mistic100/Nixie-Clock/Model 2025/indic+support.SLDASM

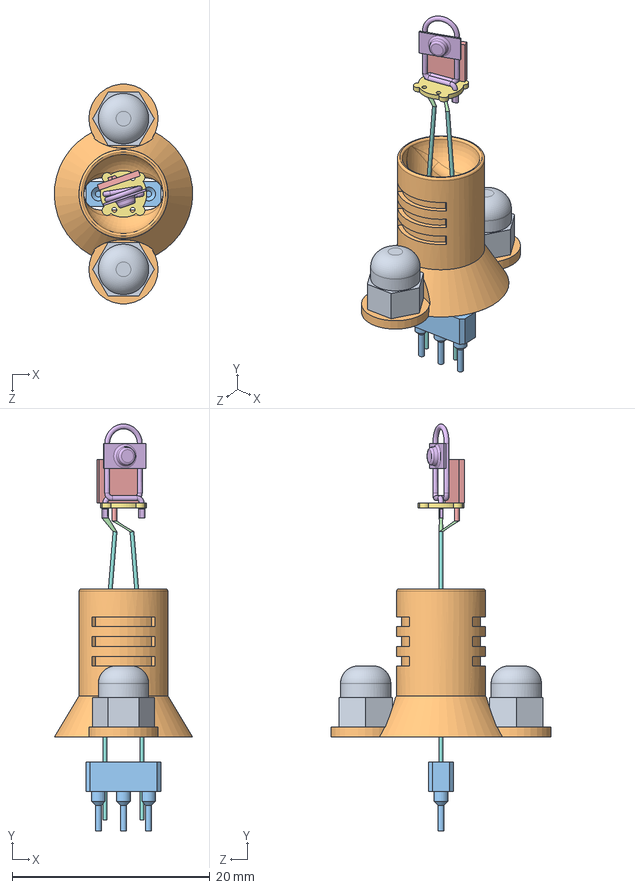
[picture p71: CAD file, 2025-04-05]
Model 2025/indic+support.SLDASM
14.0 x 41.2 x 22.2 mm
NX-SZP-IN3-02-v01 x 2
NX-SZP-IN3-03-v01
NX-SZP-IN3-04-v01
NX-SZP-IN3-05-v01
NX-SZP-IN3-06-v01
tulipex2
cache-indic
ecrou borgne x 2
