mistic100/Nixie-Clock/Model 2025/NX-SZP-IN3/NX-SZP-IN3-03-v01.SLDPRT

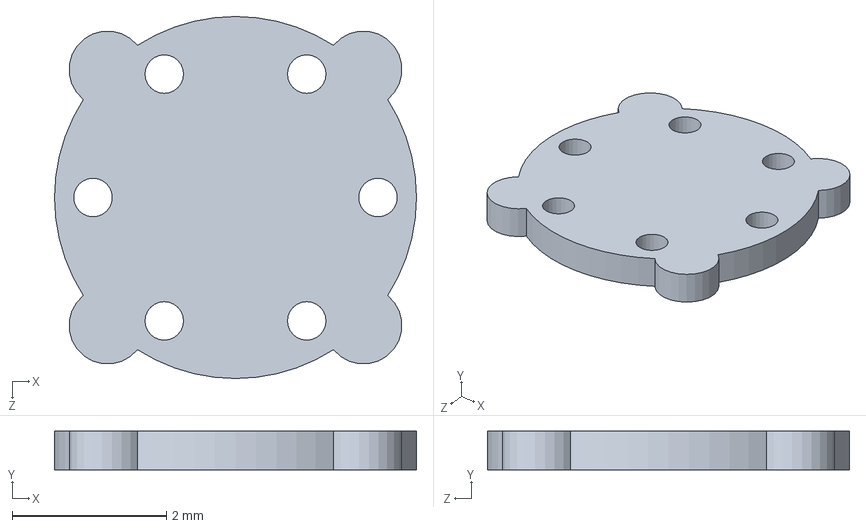
[picture p81: CAD file, 2025-04-05]
Model 2025/NX-SZP-IN3/NX-SZP-IN3-03-v01.SLDPRT
4.70 x 0.5 x 4.70 mm
