mistic100/Nixie-Clock/Model 2025/tulipex2.SLDPRT

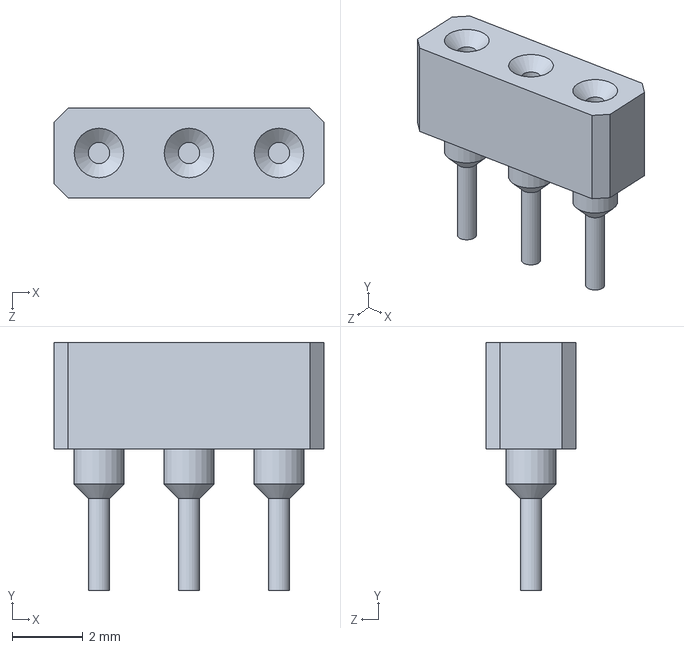
[picture p82: CAD file, 2025-04-05]
Model 2025/tulipex2.SLDPRT
7.62 x 7.00 x 2.54 mm
