mistic100/Nixie-Clock/Model 2025/calle-tube.SLDPRT

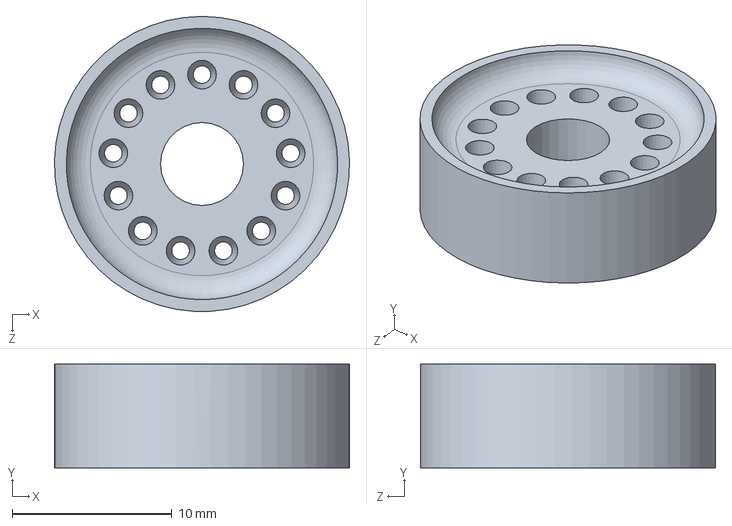
[picture p83: CAD file, 2025-04-05]
Model 2025/calle-tube.SLDPRT
18.5 x 6.50 x 18.5 mm
