mistic100/Nixie-Clock/Model 2025/NX-SZP-IN14/NX-SZP-IN14-15-v01.SLDPRT

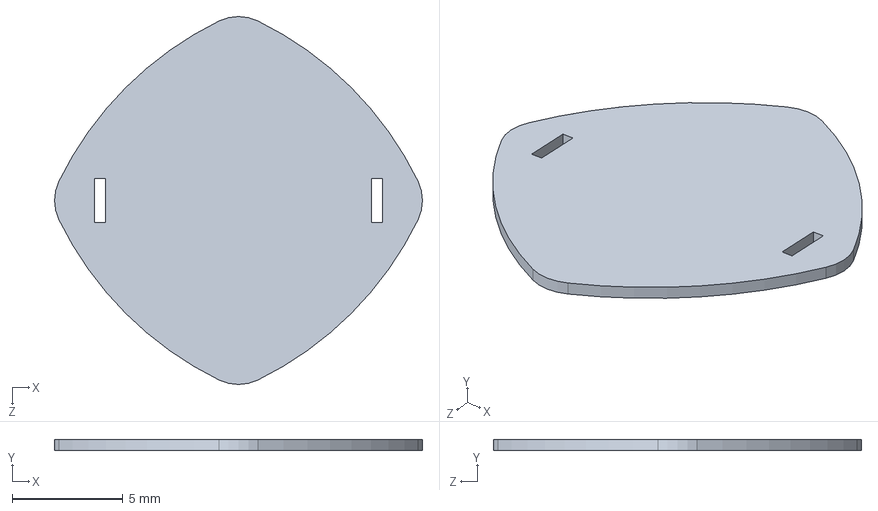
[picture p84: CAD file, 2025-04-05]
Model 2025/NX-SZP-IN14/NX-SZP-IN14-15-v01.SLDPRT
16.6 x 0.5 x 16.6 mm
