mistic100/Nixie-Clock/Model 2025/NX-SZP-IN3/NX-SZP-IN3-06-v01.SLDPRT

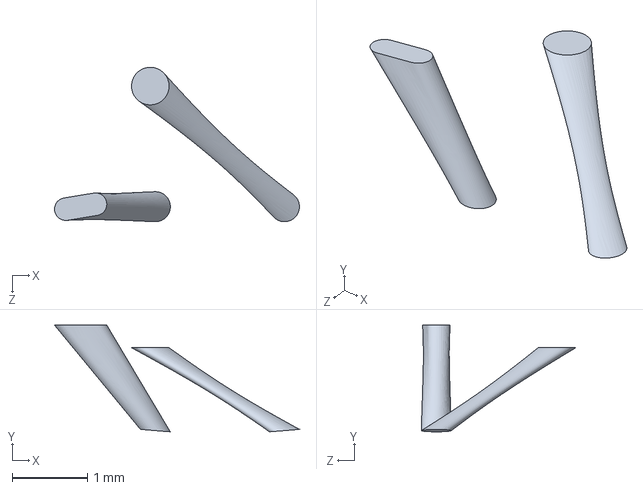
[picture p85: CAD file, 2025-04-05]
Model 2025/NX-SZP-IN3/NX-SZP-IN3-06-v01.SLDPRT
3.25 x 1.42 x 2.05 mm
