mistic100/Nixie-Clock/Model/cover.SLDPRT

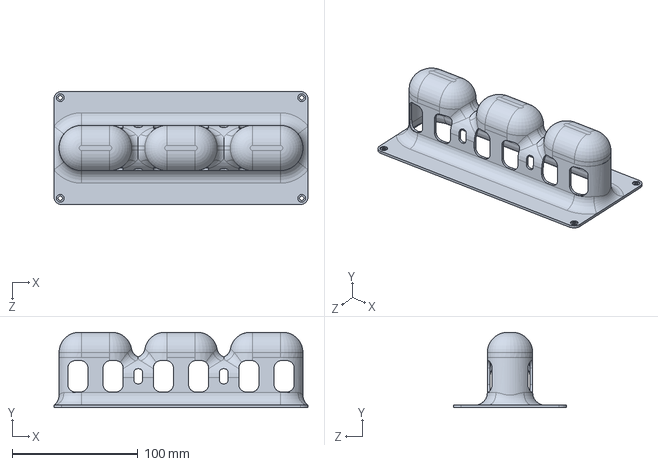
[picture p86: CAD file, 2020-09-19]
Model/cover.SLDPRT
202.0 x 60.0 x 90.0 mm
