mistic100/Nixie-Clock/Model 2025/foot.SLDPRT

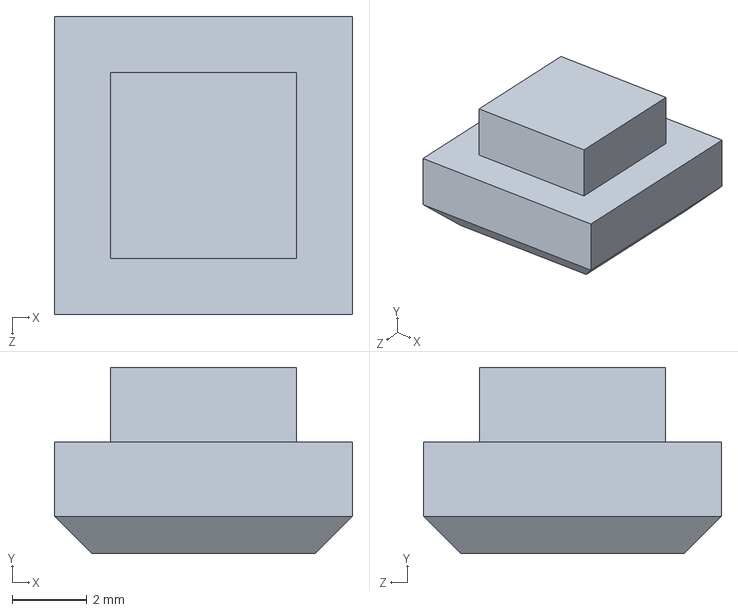
[picture p87: CAD file, 2025-04-05]
Model 2025/foot.SLDPRT
8.00 x 5.00 x 8.00 mm
