mistic100/Nixie-Clock/Model 2025/NX-SZP-IN3/NX-SZP-IN3-04-v01.SLDPRT

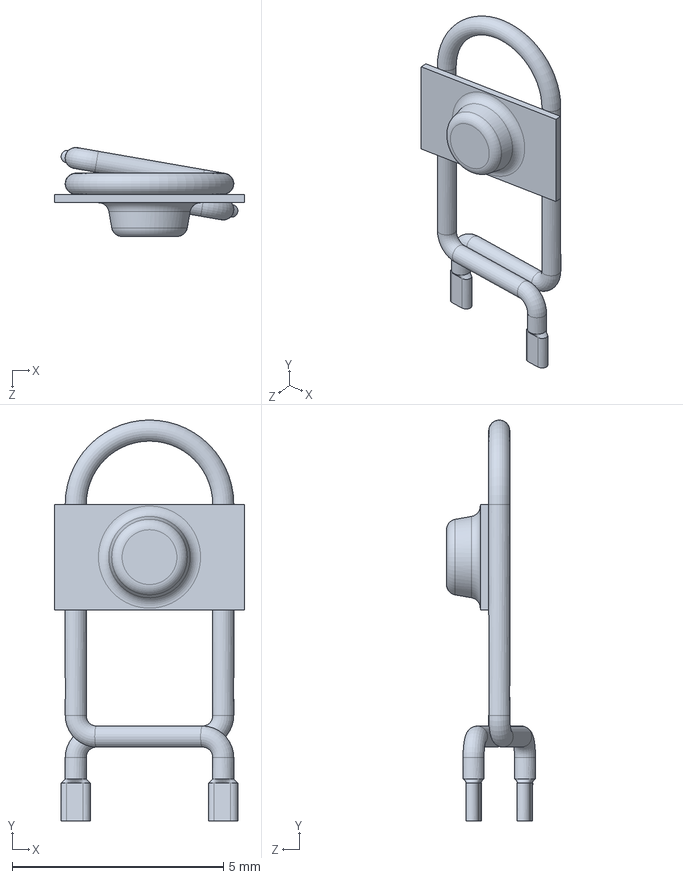
[picture p88: CAD file, 2025-04-05]
Model 2025/NX-SZP-IN3/NX-SZP-IN3-04-v01.SLDPRT
4.50 x 9.50 x 2.11 mm
