mistic100/Nixie-Clock/Model/pied.SLDPRT

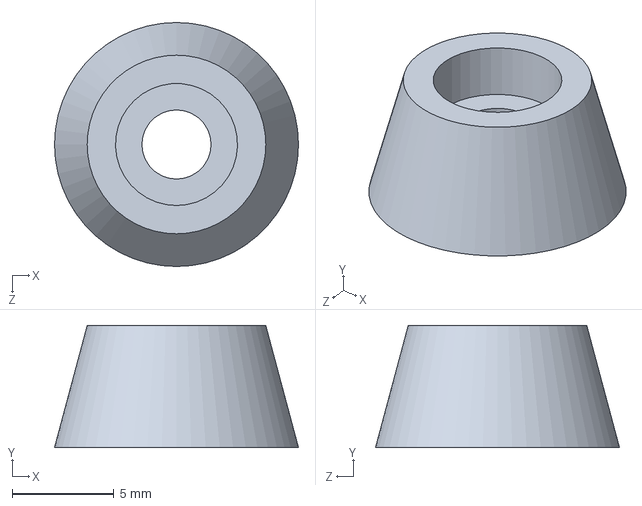
[picture p89: CAD file, 2020-06-08]
Model/pied.SLDPRT
12.0 x 6.00 x 12.0 mm
