mistic100/Nixie-Clock/Model/buttons-plate.SLDPRT

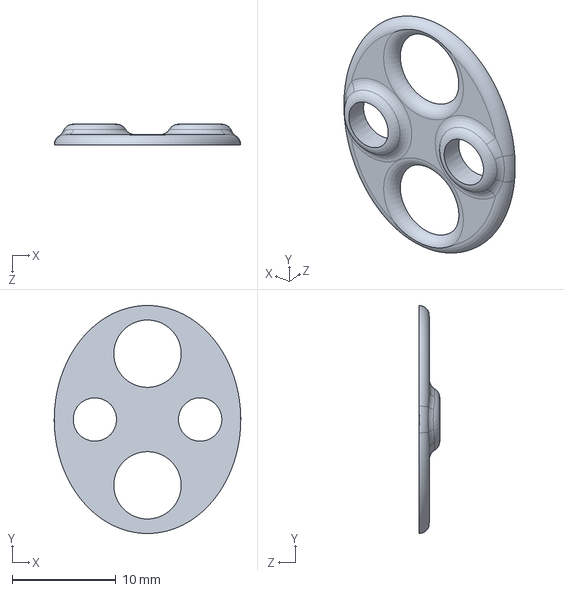
[picture p91: CAD file, 2020-06-06]
Model/buttons-plate.SLDPRT
18.0 x 22.0 x 2.00 mm
