mistic100/Nixie-Clock/Model 2025/NX-SZP-IN14/NX-SZP-IN14-20-v01.SLDPRT

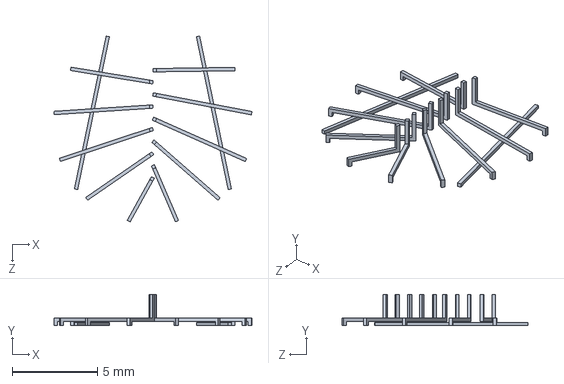
[picture p92: CAD file, 2025-04-05]
Model 2025/NX-SZP-IN14/NX-SZP-IN14-20-v01.SLDPRT
11.6 x 1.85 x 10.9 mm
