mistic100/Nixie-Clock/Model 2025/pcb.SLDPRT

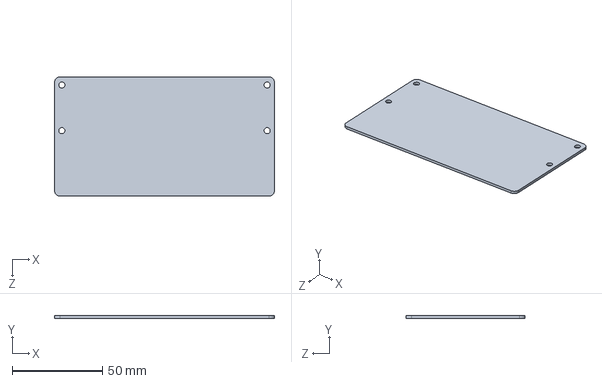
[picture p93: CAD file, 2025-04-05]
Model 2025/pcb.SLDPRT
121.6 x 1.50 x 65.9 mm
