mistic100/Nixie-Clock/Model 2025/plaque.SLDPRT

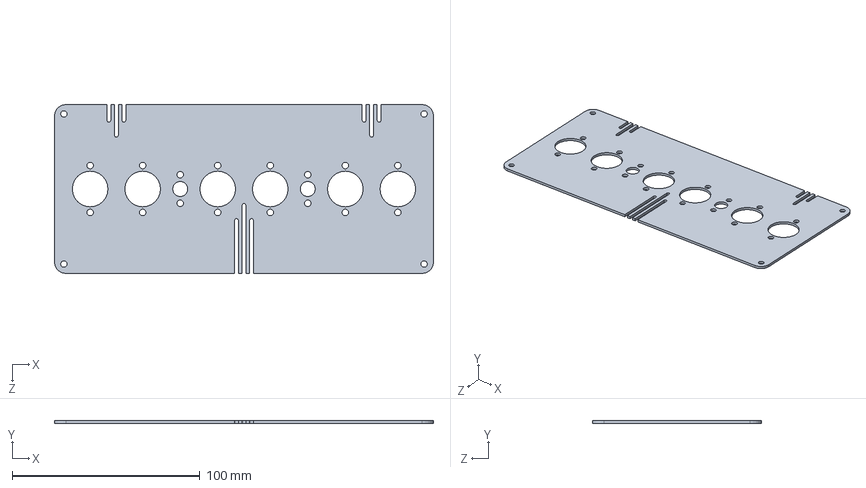
[picture p95: CAD file, 2025-04-05]
Model 2025/plaque.SLDPRT
202.0 x 1.50 x 90.0 mm
