mistic100/Nixie-Clock/Model 2025/NX-SZP-IN14/NX-SZP-IN14-19-v01.SLDPRT

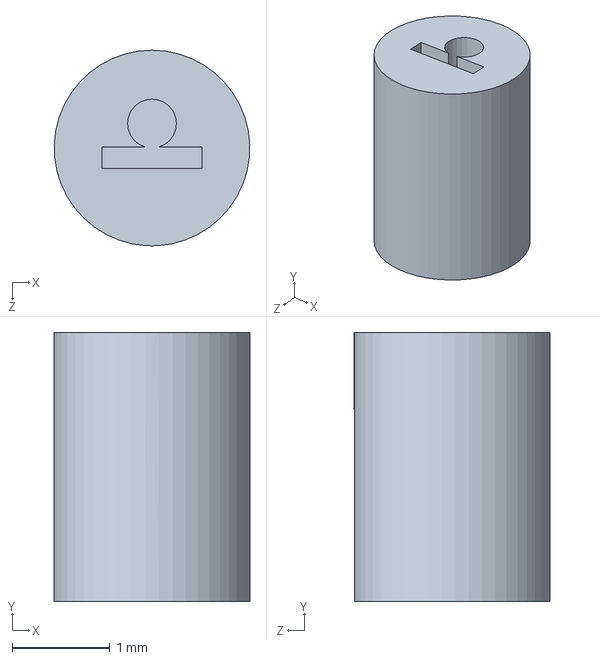
[picture p96: CAD file, 2025-04-05]
Model 2025/NX-SZP-IN14/NX-SZP-IN14-19-v01.SLDPRT
2.00 x 2.75 x 2.00 mm
