mistic100/Nixie-Clock/Model 2025/spacer-2.5.SLDPRT

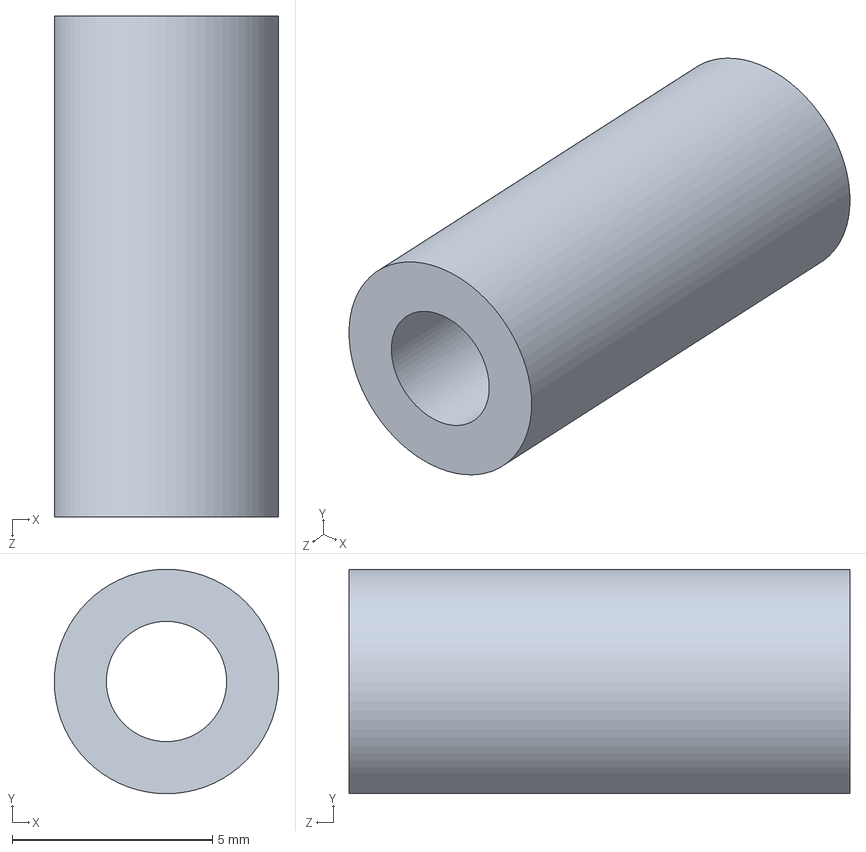
[picture p97: CAD file, 2025-04-05]
Model 2025/spacer-2.5.SLDPRT
5.60 x 5.60 x 12.5 mm
