mistic100/Nixie-Clock/Model/pcb.SLDPRT

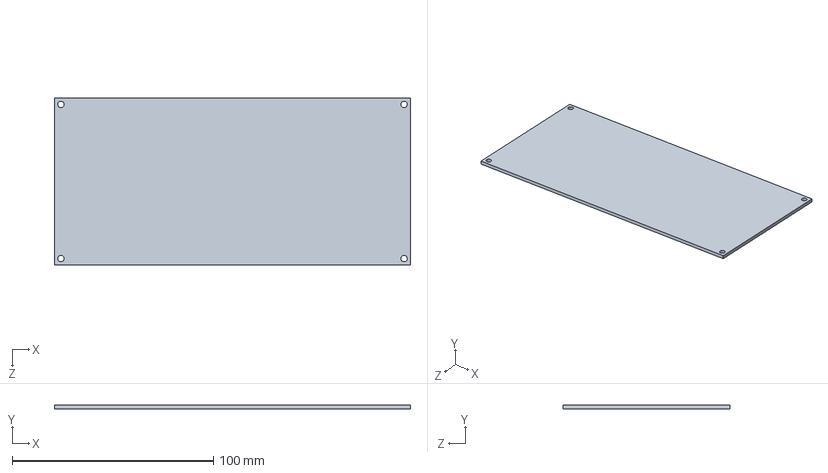
[picture p98: CAD file, 2020-05-30]
Model/pcb.SLDPRT
177.0 x 2.00 x 83.0 mm
