mistic100/Nixie-Clock/Model 2025/cache-tube.SLDPRT

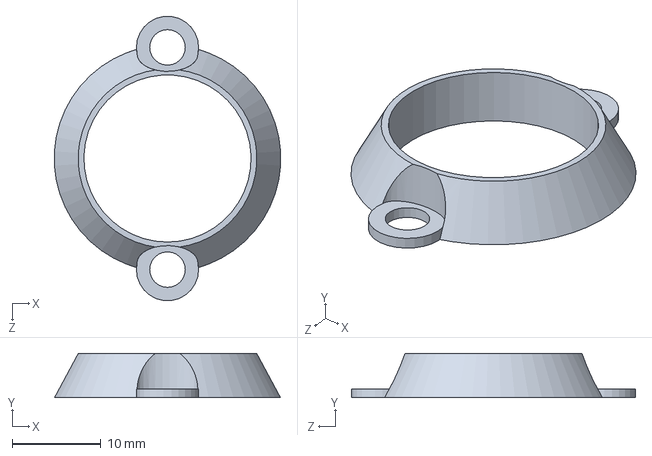
[picture p99: CAD file, 2025-04-05]
Model 2025/cache-tube.SLDPRT
25.4 x 5.00 x 31.9 mm
