mistic100/Nixie-Clock/Model/led-strip.SLDPRT

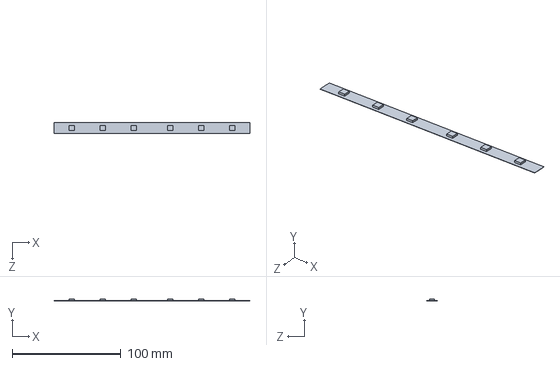
[picture p101: CAD file, 2020-05-30]
Model/led-strip.SLDPRT
180.0 x 1.70 x 10.0 mm
