mistic100/Nixie-Clock/Model 2025/NX-SZP-IN14/NX-SZP-IN14-02-v01.SLDPRT

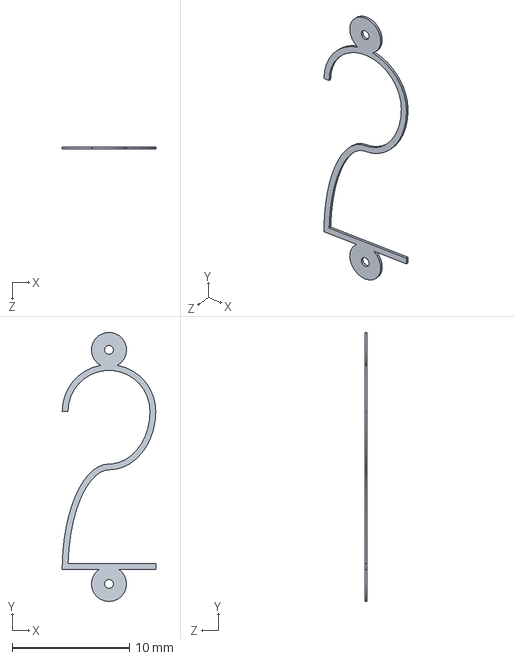
[picture p102: CAD file, 2025-04-05]
Model 2025/NX-SZP-IN14/NX-SZP-IN14-02-v01.SLDPRT
8.00 x 23.0 x 0.2 mm
