mistic100/Nixie-Clock/Model 2025/cache-indic.SLDPRT

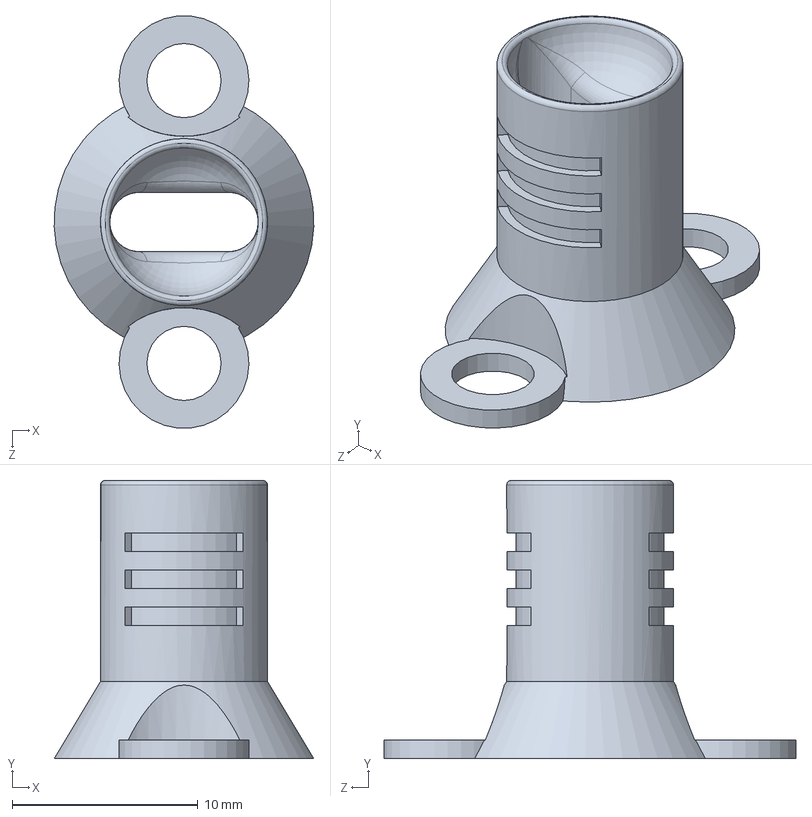
[picture p103: CAD file, 2025-04-05]
Model 2025/cache-indic.SLDPRT
14.0 x 15.0 x 22.2 mm
