mistic100/Nixie-Clock/Model/touch-button.SLDPRT

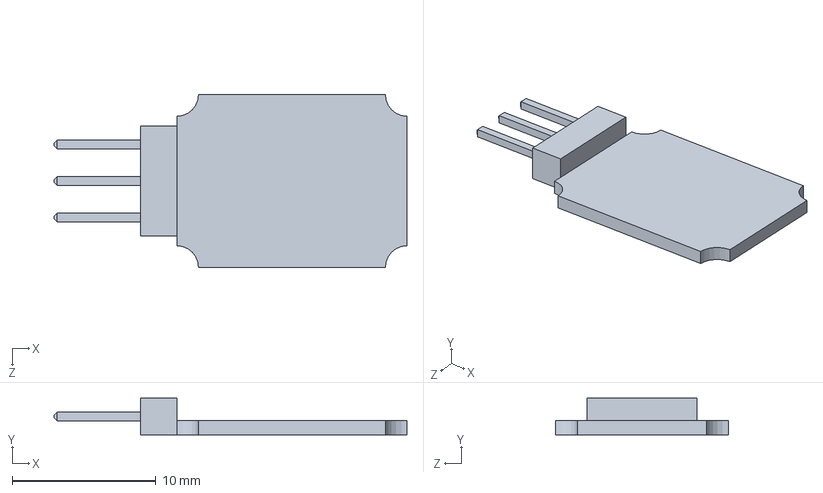
[picture p105: CAD file, 2020-05-30]
Model/touch-button.SLDPRT
24.5 x 2.54 x 12.0 mm
