mistic100/Nixie-Clock/Model 2025/NX-SZP-IN14/NX-SZP-IN14-14-v01.SLDPRT

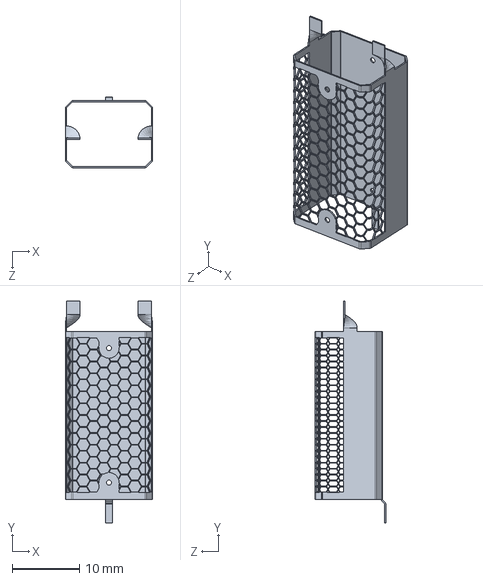
[picture p106: CAD file, 2025-04-05]
Model 2025/NX-SZP-IN14/NX-SZP-IN14-14-v01.SLDPRT
13.0 x 33.0 x 10.5 mm
