mistic100/Nixie-Clock/Model 2025/support-buttons.SLDPRT

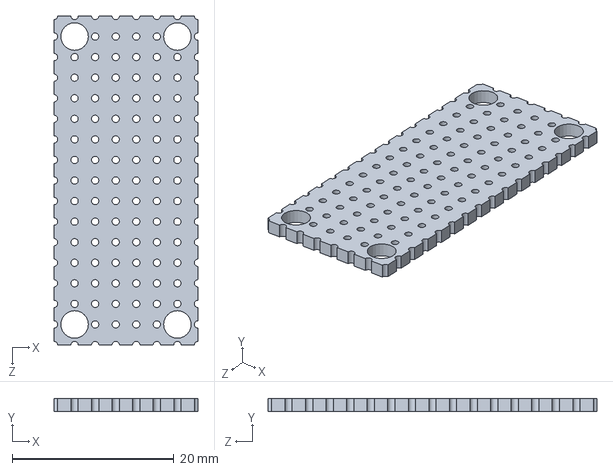
[picture p107: CAD file, 2025-04-05]
Model 2025/support-buttons.SLDPRT
17.8 x 1.60 x 40.6 mm
