mistic100/Nixie-Clock/Model/ecrou borgne.SLDPRT

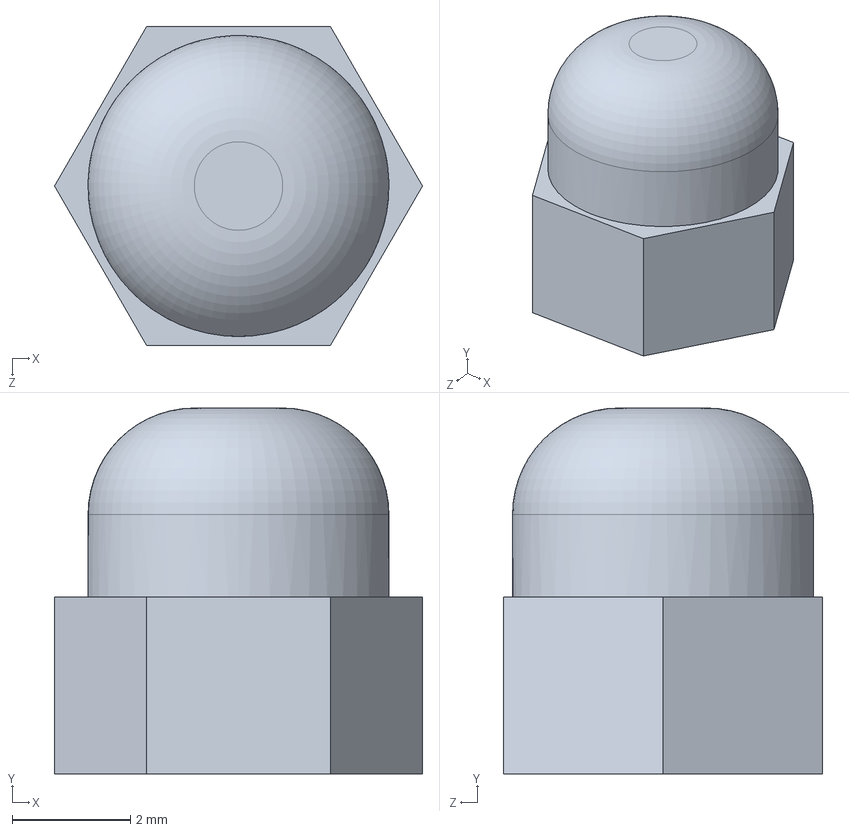
[picture p108: CAD file, 2020-05-30]
Model/ecrou borgne.SLDPRT
6.24 x 6.20 x 5.40 mm
