mistic100/Nixie-Clock/Model 2025/jack.SLDPRT

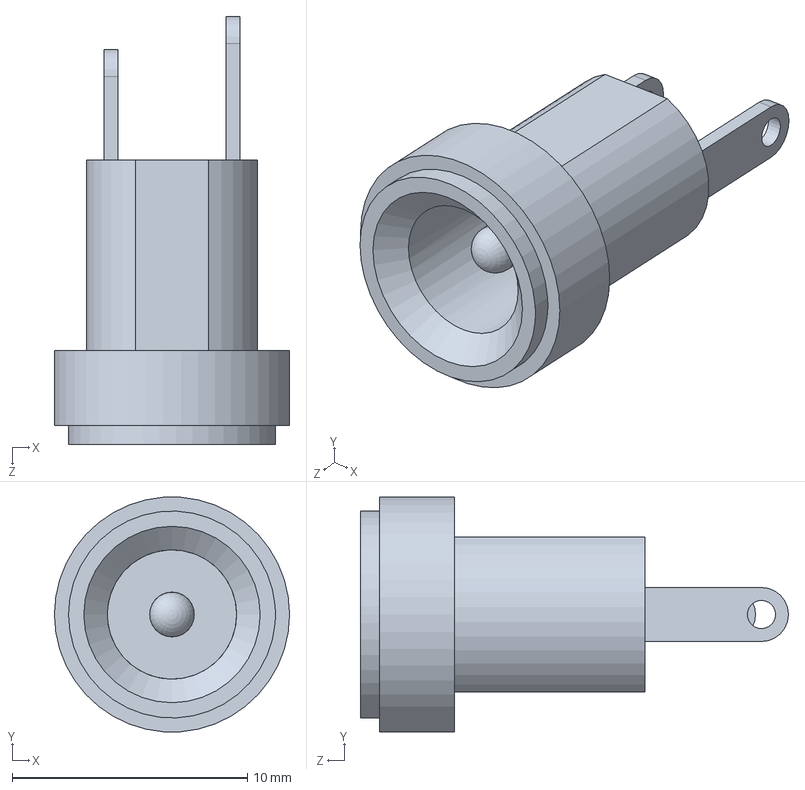
[picture p109: CAD file, 2025-04-05]
Model 2025/jack.SLDPRT
10.0 x 9.97 x 18.2 mm
