mistic100/Nixie-Clock/Model 2025/NX-SZP-IN14/NX-SZP-IN14-11-v01.SLDPRT

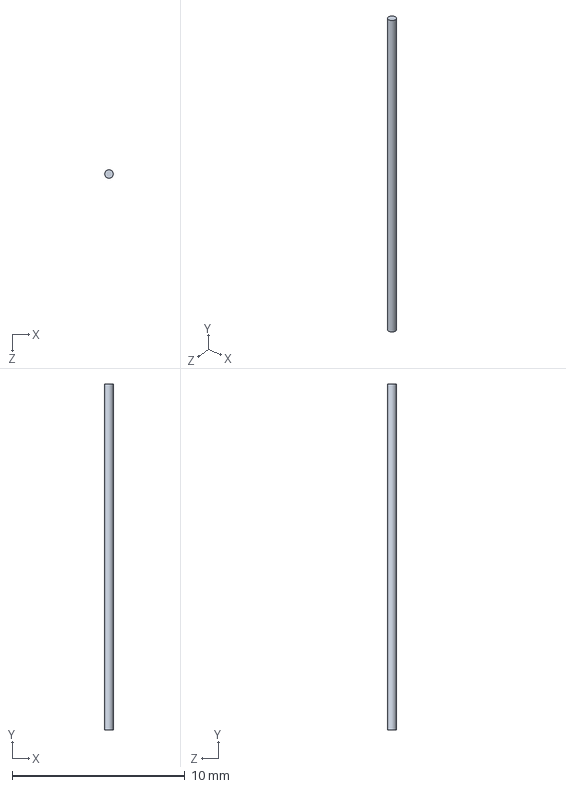
[picture p110: CAD file, 2025-04-05]
Model 2025/NX-SZP-IN14/NX-SZP-IN14-11-v01.SLDPRT
0.5 x 20.0 x 0.5 mm
