mistic100/Nixie-Clock/Model/header.SLDPRT

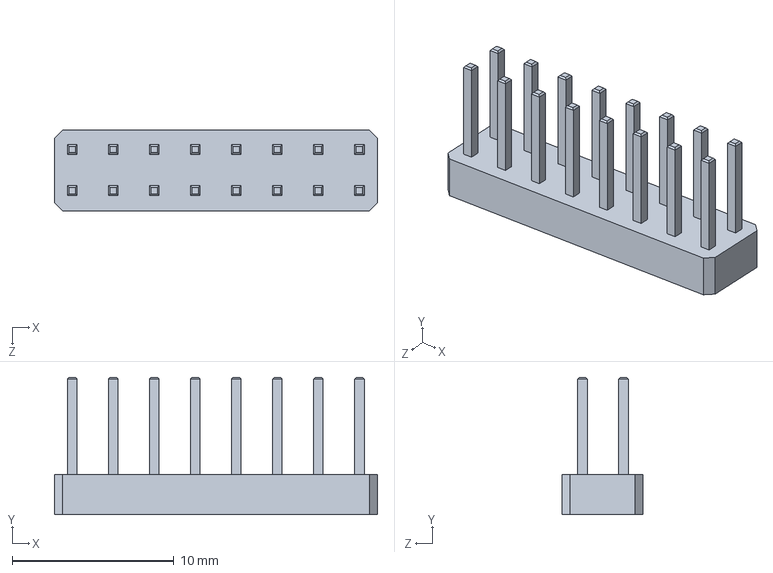
[picture p111: CAD file, 2020-05-30]
Model/header.SLDPRT
20.0 x 8.50 x 5.00 mm
