mistic100/Nixie-Clock/Model 2025/NX-SZP-IN14/NX-SZP-IN14-21-v02.SLDPRT

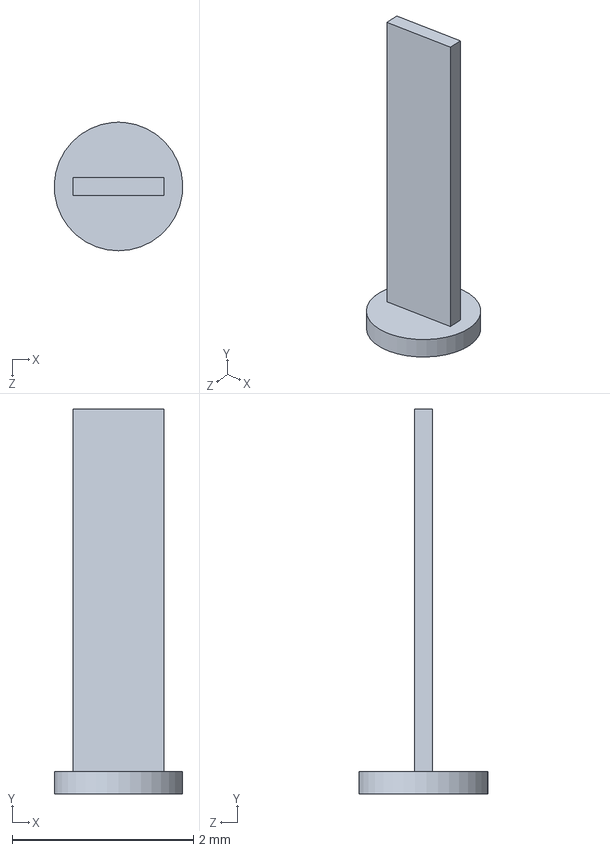
[picture p112: CAD file, 2025-04-05]
Model 2025/NX-SZP-IN14/NX-SZP-IN14-21-v02.SLDPRT
1.42 x 4.25 x 1.42 mm
