mistic100/Nixie-Clock/Model 2025/NX-SZP-IN14/NX-SZP-IN14-10-v01.SLDPRT

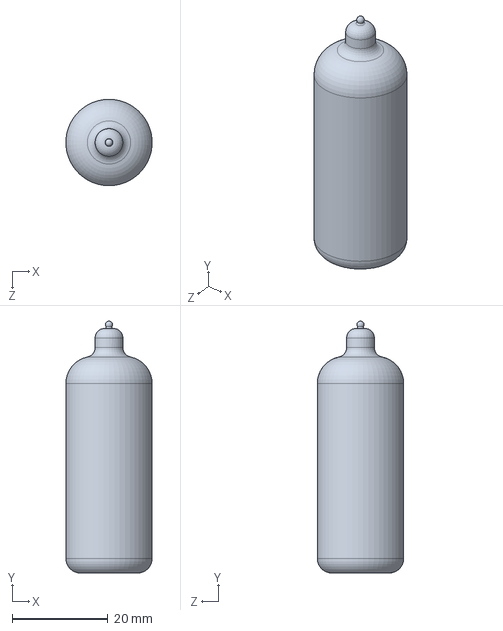
[picture p113: CAD file, 2025-04-05]
Model 2025/NX-SZP-IN14/NX-SZP-IN14-10-v01.SLDPRT
18.0 x 52.5 x 18.0 mm
