mistic100/Nixie-Clock/Model 2025/front-button.SLDPRT

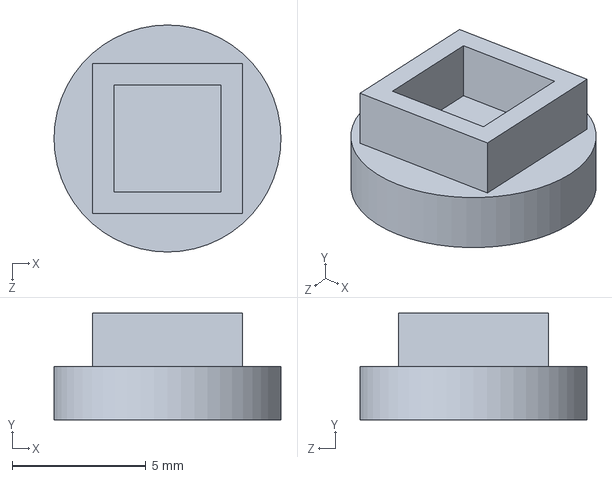
[picture p114: CAD file, 2025-04-05]
Model 2025/front-button.SLDPRT
8.50 x 4.00 x 8.50 mm
