mistic100/Nixie-Clock/Model 2025/support-indic.SLDPRT

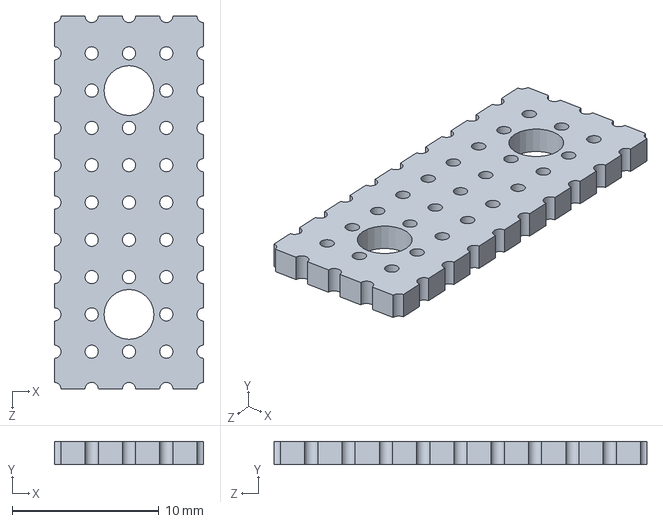
[picture p116: CAD file, 2025-04-05]
Model 2025/support-indic.SLDPRT
10.2 x 1.60 x 25.4 mm
