mistic100/Nixie-Clock/Model 2025/NX-SZP-IN14/NX-SZP-IN14-12-v01.SLDPRT

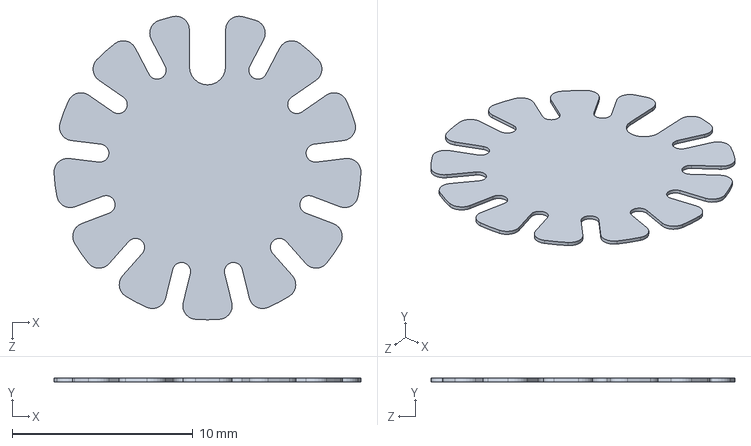
[picture p117: CAD file, 2025-04-05]
Model 2025/NX-SZP-IN14/NX-SZP-IN14-12-v01.SLDPRT
17.0 x 0.2 x 16.8 mm
