mistic100/Nixie-Clock/Model 2025/pcb2.SLDPRT

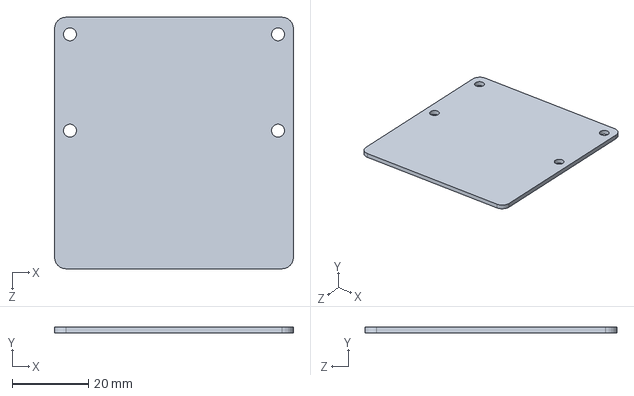
[picture p118: CAD file, 2025-04-05]
Model 2025/pcb2.SLDPRT
62.6 x 1.50 x 65.9 mm
