mistic100/Nixie-Clock/Model 2025/NX-SZP-IN14/NX-SZP-IN14-13-v01.SLDPRT

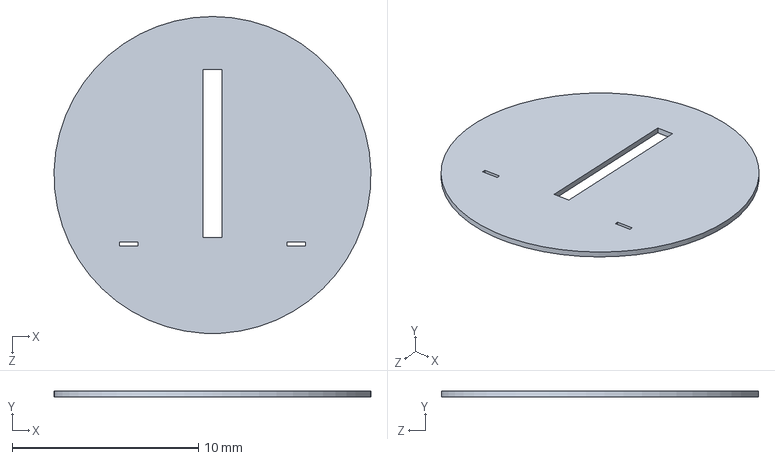
[picture p119: CAD file, 2025-04-05]
Model 2025/NX-SZP-IN14/NX-SZP-IN14-13-v01.SLDPRT
17.0 x 0.3 x 17.0 mm
