mistic100/Nixie-Clock/Model/support-buttons.SLDPRT

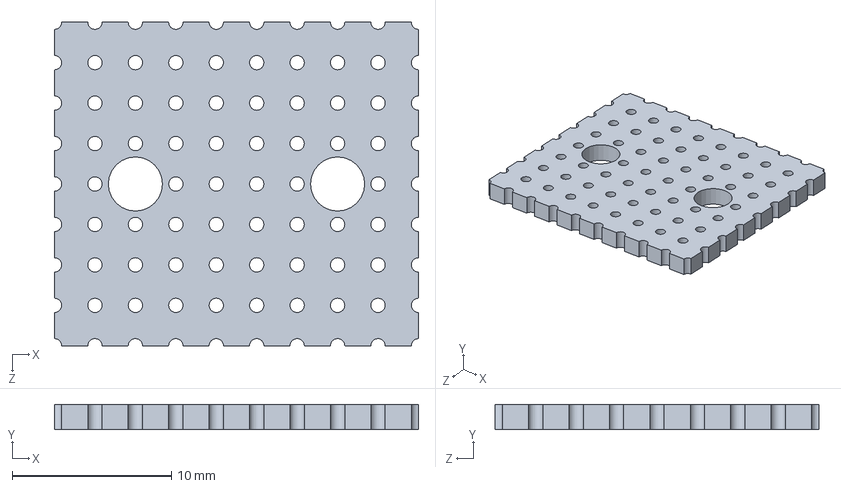
[picture p120: CAD file, 2020-05-30]
Model/support-buttons.SLDPRT
22.9 x 1.60 x 20.3 mm
