mistic100/Nixie-Clock/Model 2025/coque2.SLDPRT

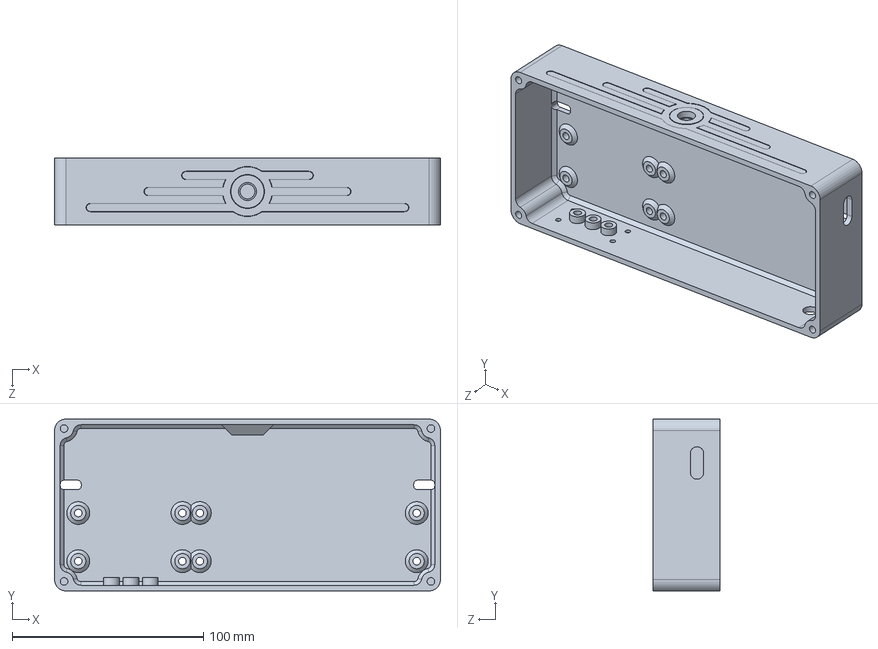
[picture p121: CAD file, 2025-04-05]
Model 2025/coque2.SLDPRT
202.0 x 90.0 x 35.0 mm
