mistic100/Nixie-Clock/Model 2025/NX-SZP-IN14/NX-SZP-IN14-16-v01.SLDPRT

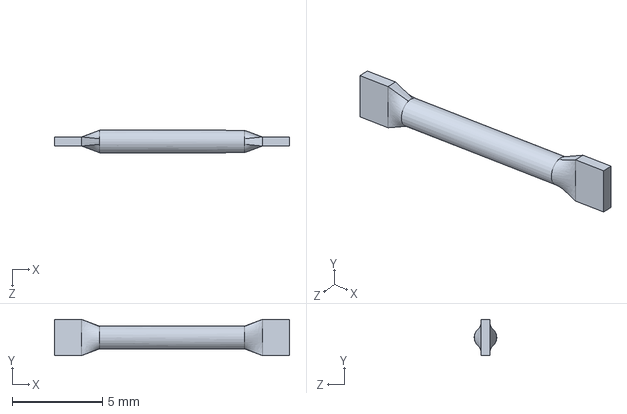
[picture p123: CAD file, 2025-04-05]
Model 2025/NX-SZP-IN14/NX-SZP-IN14-16-v01.SLDPRT
13.0 x 2.00 x 1.25 mm
