mistic100/Nixie-Clock/Model/powerin.SLDPRT

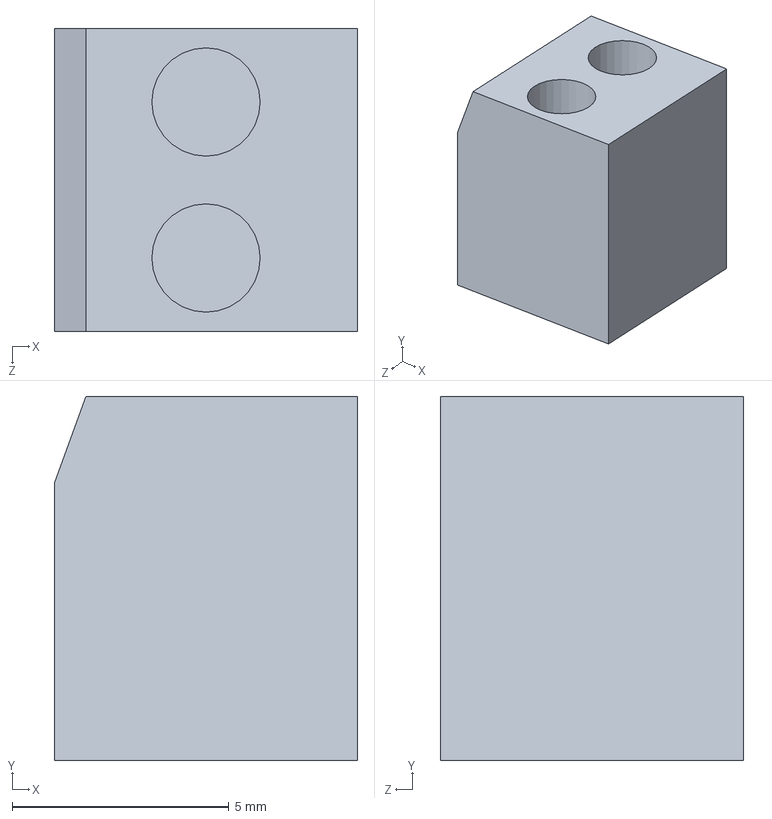
[picture p124: CAD file, 2020-05-30]
Model/powerin.SLDPRT
7.00 x 8.40 x 7.00 mm
