mistic100/Nixie-Clock/Model/bouton.SLDPRT

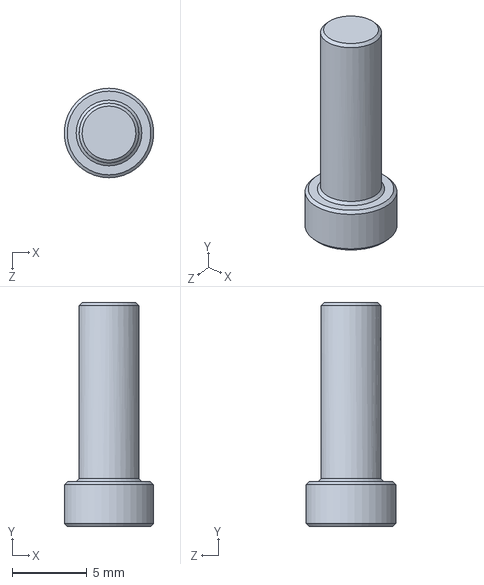
[picture p126: CAD file, 2020-05-30]
Model/bouton.SLDPRT
5.98 x 15.0 x 6.00 mm
