mistic100/Nixie-Clock/Model 2025/button-support.SLDASM

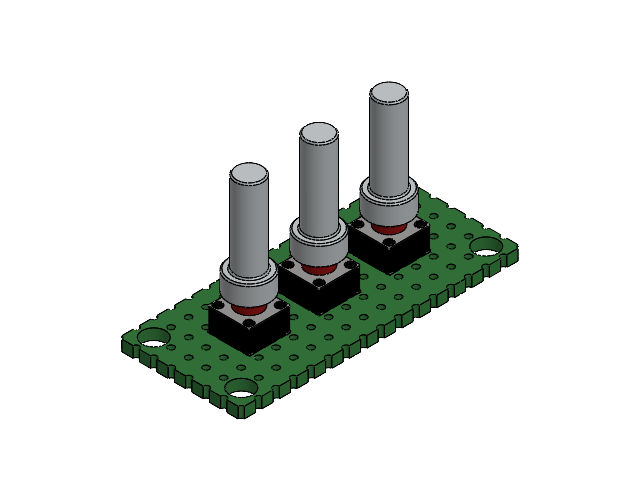
[picture p127: CAD file, 2025-04-05]
Model 2025/button-support.SLDASM
support-buttons
bouton x 3
6x6 mm x 3
